fcte-pi1/2026_1_PI1_Grupo02_Bruno/hw/Divisor de Tensão/EsquematicoDivisorDeTensao.png

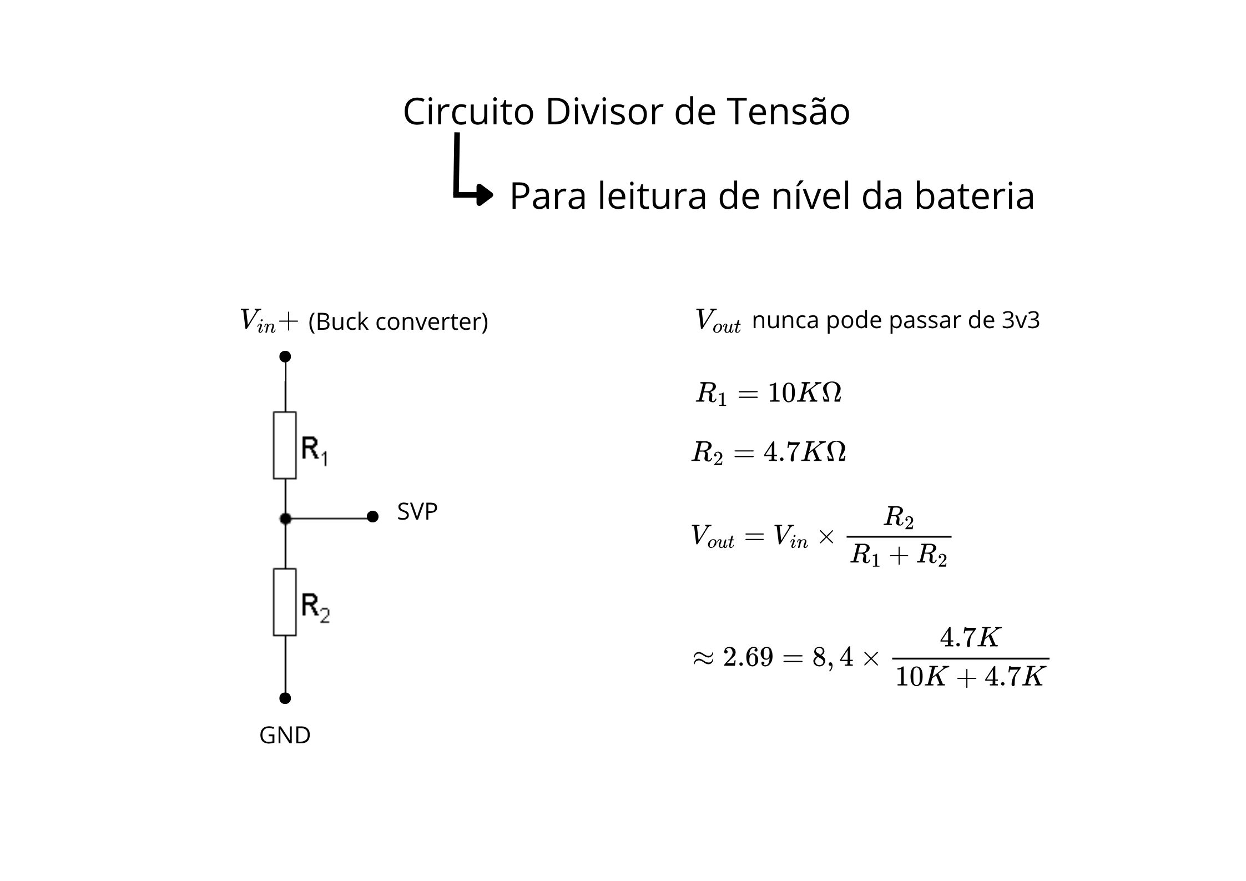
hw/Divisor de Tensão/EsquematicoDivisorDeTensao.png
