fcte-pi1/2026_1_PI1_Grupo02_Bruno/hw/esquematico_geral.png

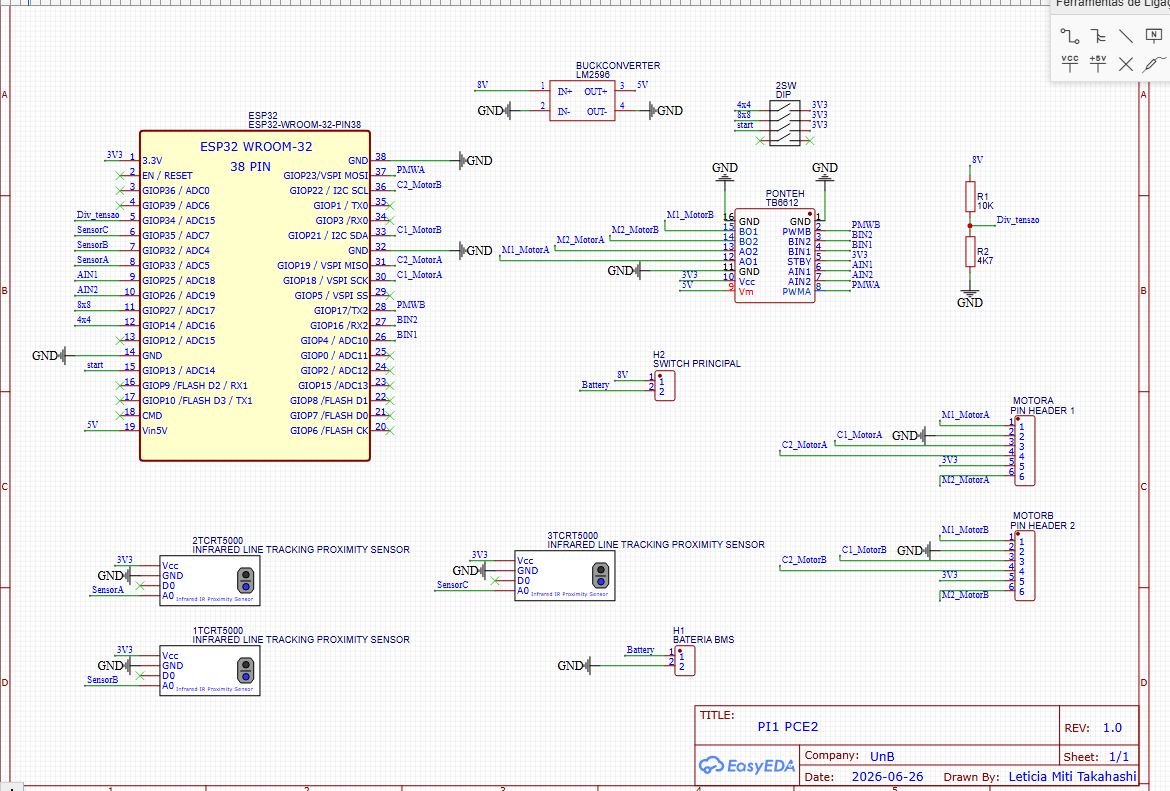
hw/esquematico_geral.png
