fcte-pi1/2026_1_PI1_Grupo02_Bruno/hw/Update na Lógica de Alimentação/EsquematicoSwitchMestre.png

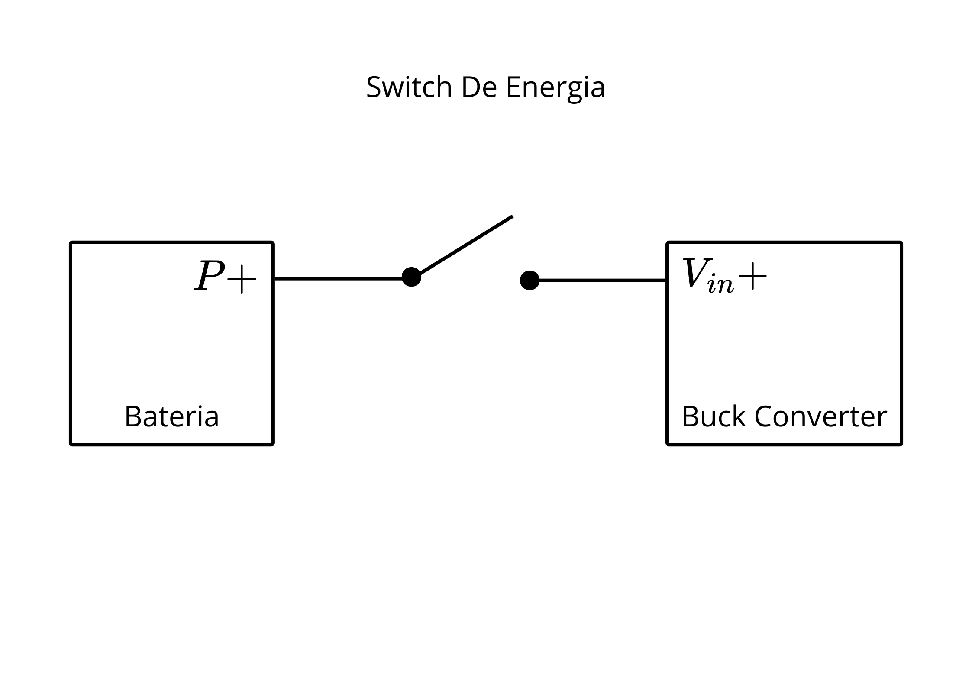
hw/Update na Lógica de Alimentação/EsquematicoSwitchMestre.png
