fcte-pi1/2026_1_PI1_Grupo02_Bruno/mec/Robô/media/chassi e rodas.jpeg

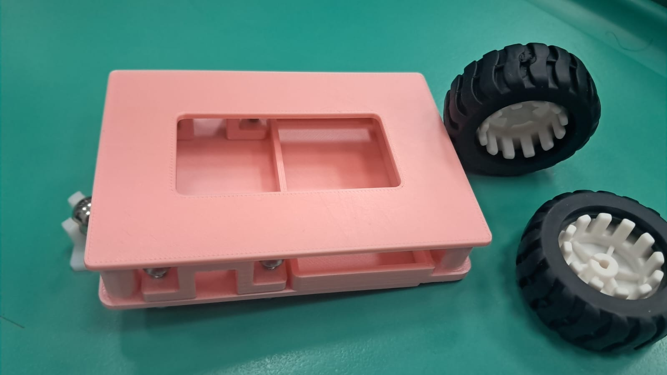
mec/Robô/media/chassi e rodas.jpeg
