fcte-pi1/2026_1_PI1_Grupo02_Bruno/mec/Robô/media/Chassi parafusado.jpeg

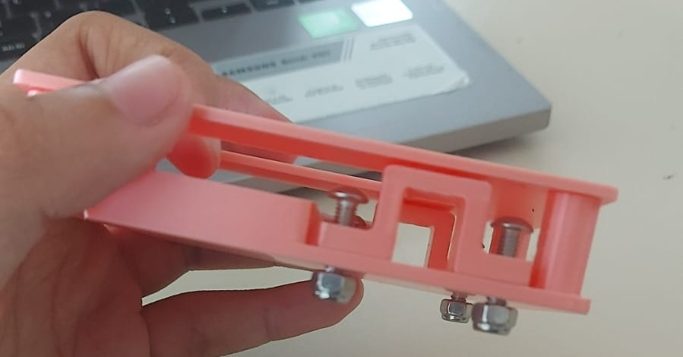
mec/Robô/media/Chassi parafusado.jpeg
