fcte-pi1/2026_1_PI1_Grupo02_Bruno/hw/Componentes/Comprovantes dos Componentes/ComprovanteESP.jpeg

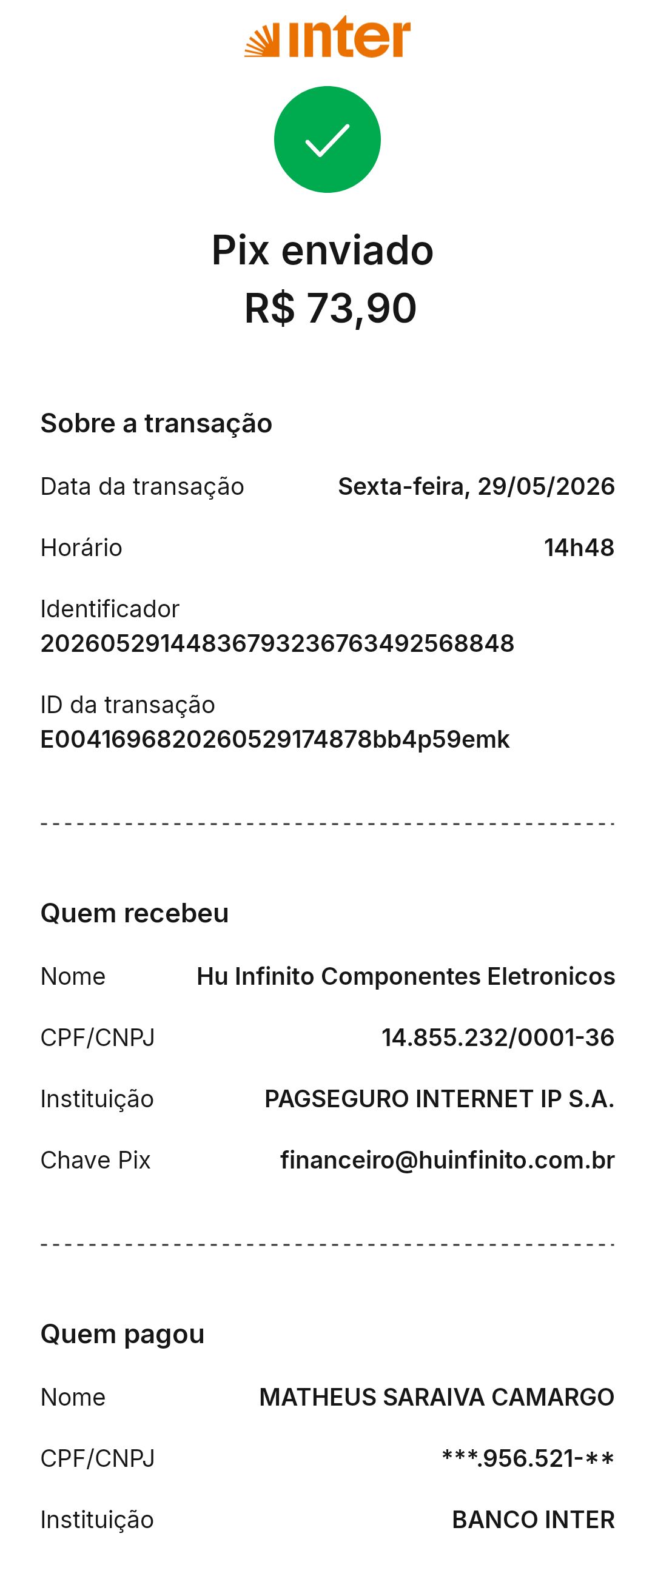
hw/Componentes/Comprovantes dos Componentes/ComprovanteESP.jpeg
