fcte-pi1/2026_1_PI1_Grupo02_Bruno/hw/Componentes/ModeloESP32.jpg

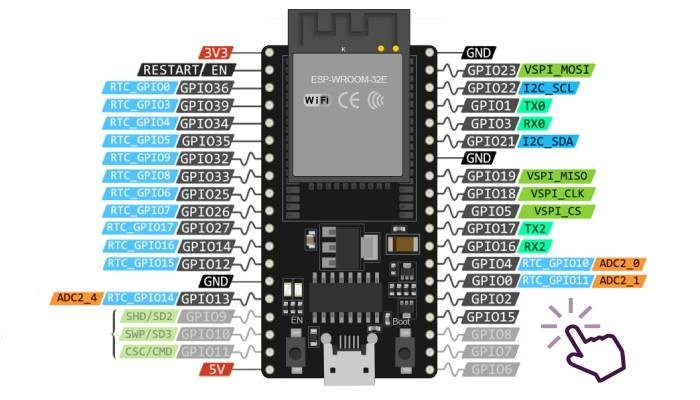
hw/Componentes/ModeloESP32.jpg
