fcte-pi1/2026_1_PI1_Grupo02_Bruno/hw/Teste De Alimentação/EsquematicoAlimentacao.png

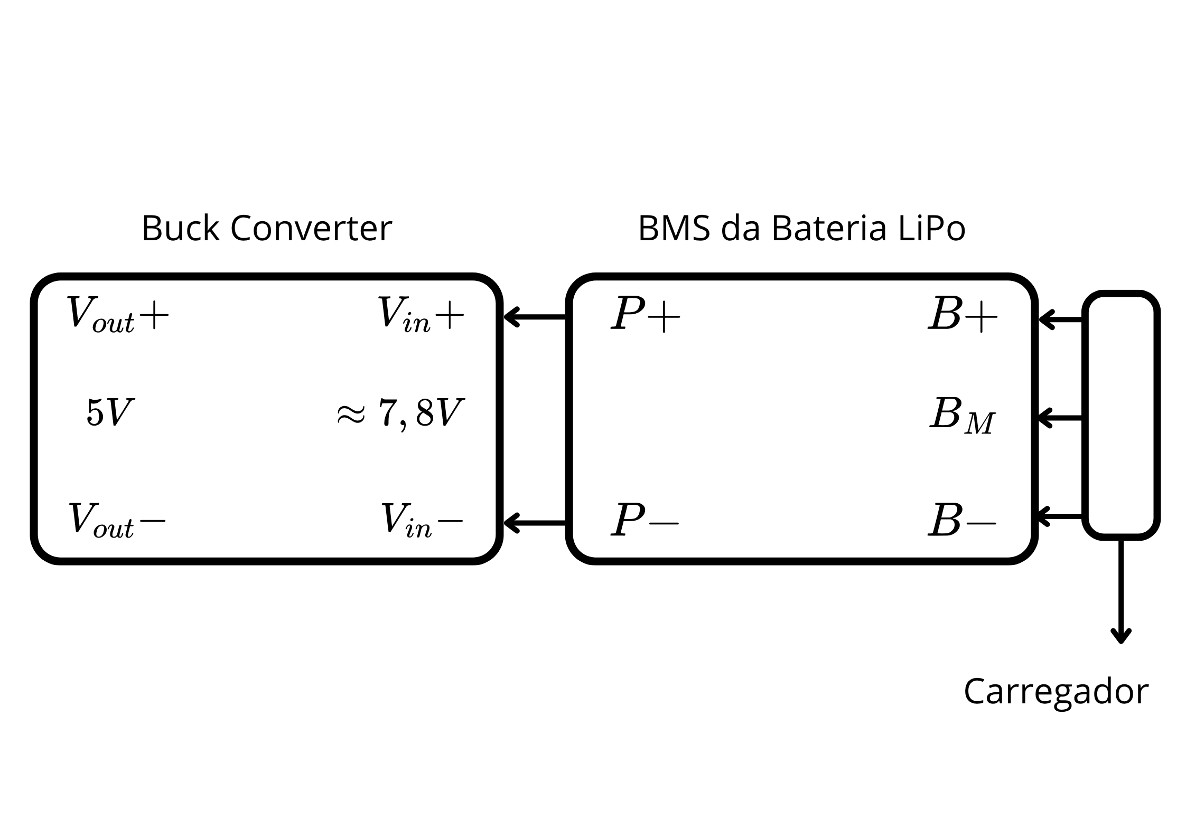
hw/Teste De Alimentação/EsquematicoAlimentacao.png
