fcte-pi1/2026_1_PI1_Grupo02_Bruno/hw/Teste dos Motores, Encoders e Ponte H/Esquematico_Motores_E_PonteH.png

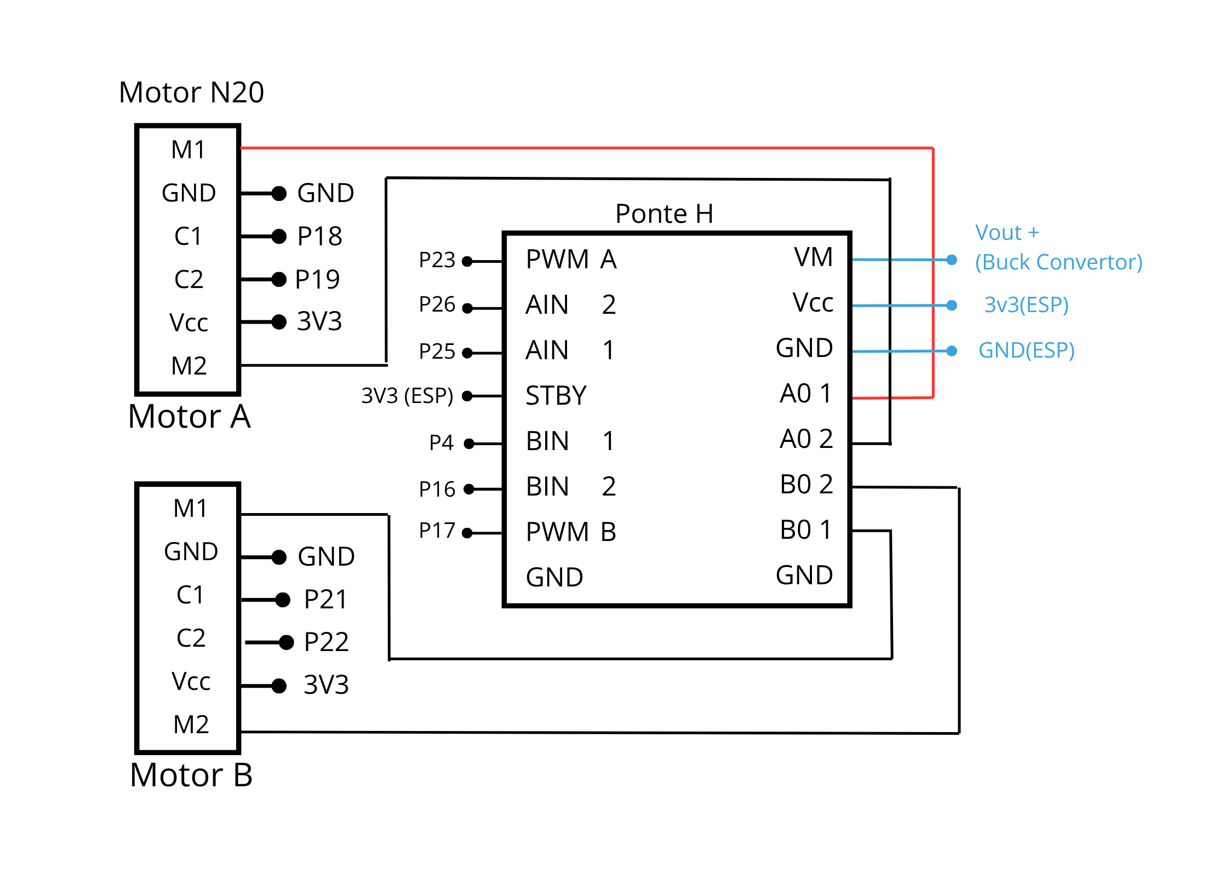
hw/Teste dos Motores, Encoders e Ponte H/Esquematico_Motores_E_PonteH.png
