fcte-pi1/2026_1_PI1_Grupo02_Bruno/hw/Mapeamento da ESP/EsquematicoESP.pdf

5V

## CND

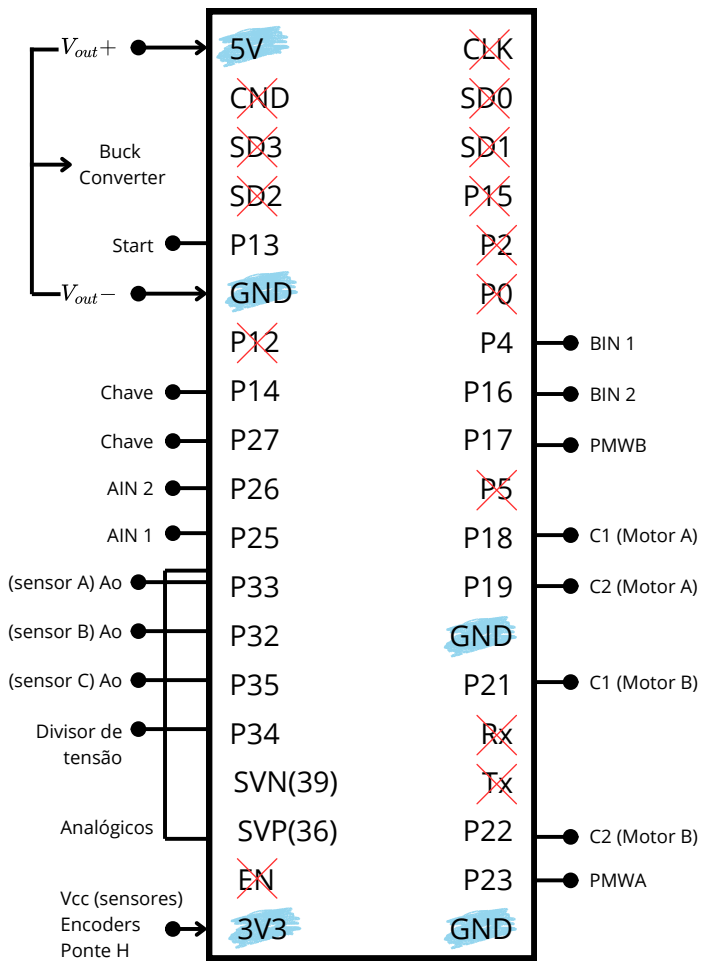
[picture p49: page 1]
