fcte-pi1/2026_1_PI1_Grupo02_Bruno/hw/Mapeamento da ESP/PortasAnalogicas.pdf

## Portas Analógicas

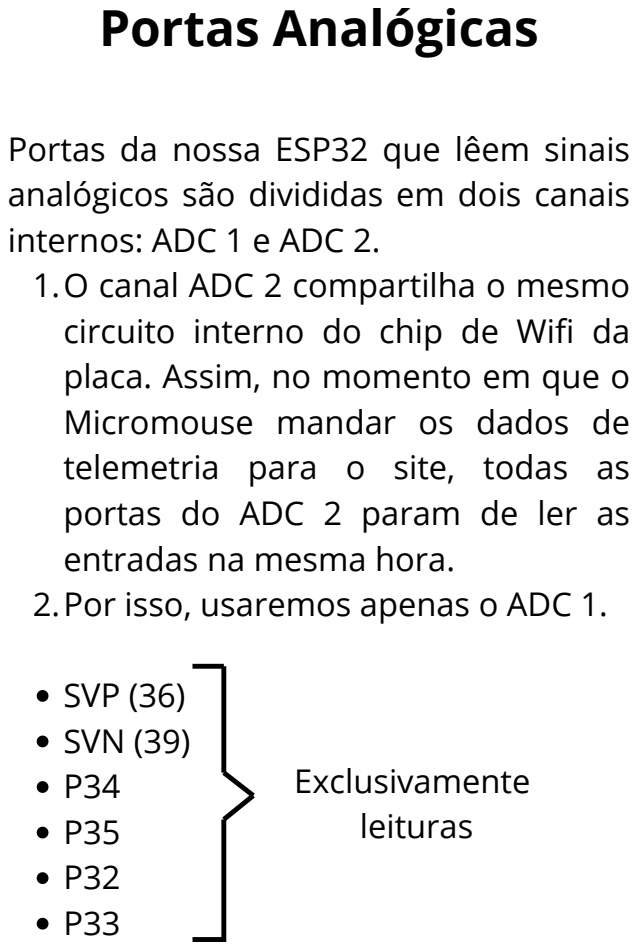
[picture p50: page 1]
SVP (36) SVN (39) P34 P35 P32 P33; Exclusivamente leituras

Portas da nossa ESP32 que lêem sinais
analógicos são divididas em dois canais
internos: ADC 1 e ADC 2.
1.O canal ADC 2 compartilha o mesmo
circuito interno do chip de Wifi da
placa. Assim, no momento em que o
Micromouse mandar os dados de
telemetria para o site, todas as
portas do ADC 2 param de ler as
entradas na mesma hora.
2.Por isso, usaremos apenas o ADC 1.
