fcte-pi1/2026_1_PI1_Grupo02_Bruno/mec/Desenho Técnico/Robô/Explode_Sheet_1.pdf

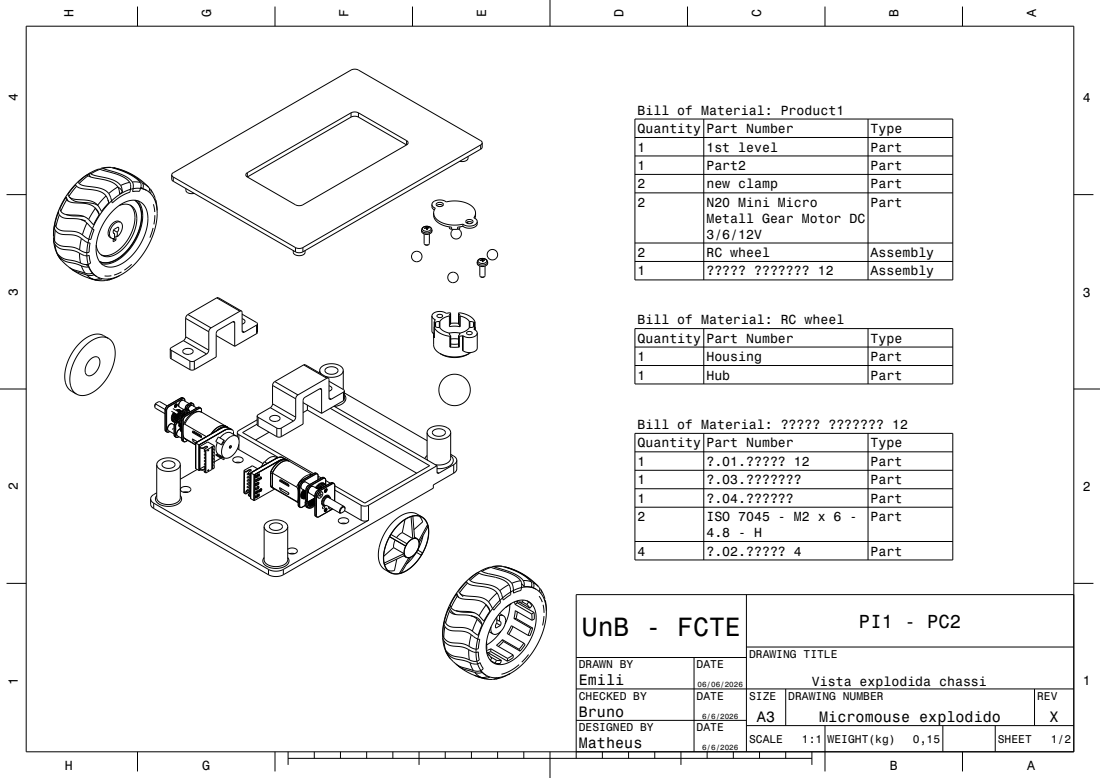
[picture p51: page 1]
DRAWING TITLE; UnB - FCTE

Bill of Material: Product1

Quantity | Part Number | Type
1 | 1st level | Part
1 | Part2 | Part
2 | new clamp | Part
2 | N20 Mini Micro Metall Gear Motor DC 3/6/12V | Part

2 | RC wheel | Assembly
1 | ????? ??????? 12 | Assembly

Bill of Material: RC wheel

1 | Housing | Part
1 | Hub | Part

Bill of Material: ????? ??????? 12

1 | ?.01.????? 12 | Part
1 | ?.03.??????? | Part
1 | ?.04.?????? | Part
2 | ISO 7045 - M2 x 6 -4.8 - H | Part

4 | ?.02.????? 4 | Part

DRAWN BY Emili | DATE 06/06/2026

Vista explodida chassi

CHECKED BY Bruno | DATE 6/6/2026 | SIZE A3 | DRAWING NUMBER Micromouse explodido | REV X

DESIGNED BY Matheus | DATE 6/6/2026

SCALE 1:1 | WEIGHT(kg) 0,15 | SHEET 1/2
