fcte-pi1/2026_1_PI1_Grupo02_Bruno/mec/Desenho Técnico/Labirinto/Labirinto Draft.pdf

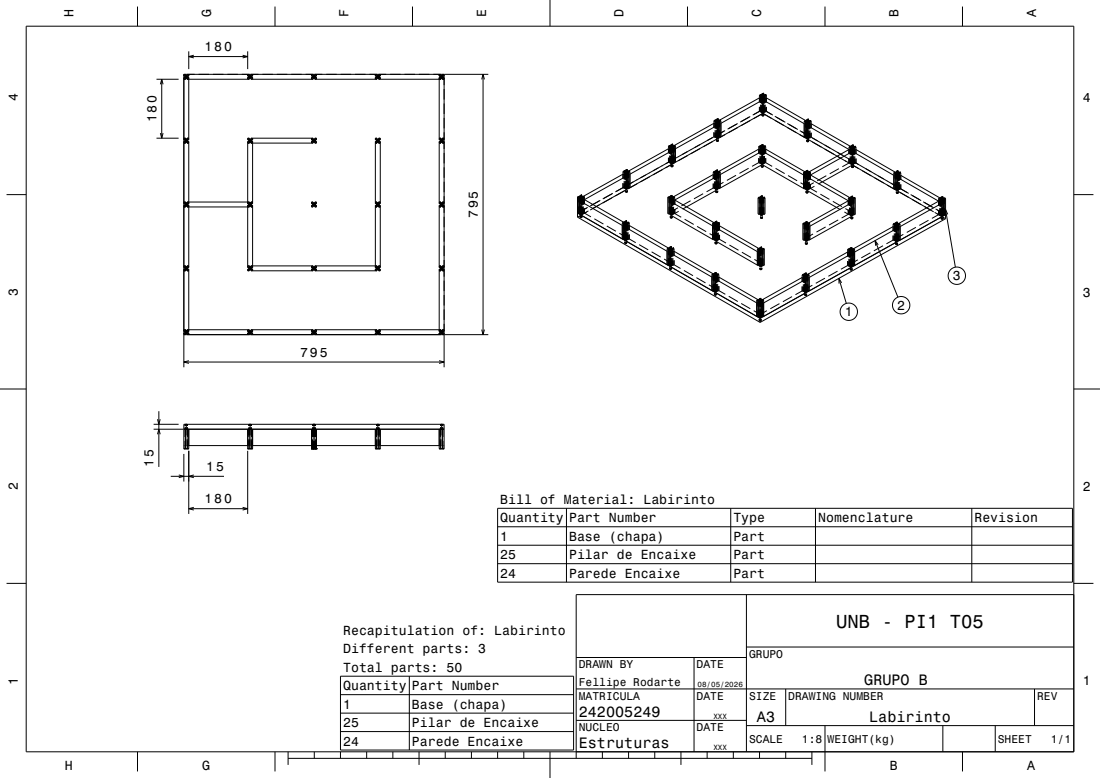
[picture p52: page 1]
DRAWN BY Fellipe Rodarte; SCALE; 1:8 WEIGHT(kg); SHEET; DRAWING NUMBER; Quantity Part Number; Type; Nomenclature; Revision; Base (chapa); Part; Pilar de Encaixe; Parede Encaixe; GRUPO B; UNB - PI1 T05

Bill of Material: Labirinto

Recapitulation of: Labirinto
Different parts: 3
Total parts: 50
Quantity Part Number
