fcte-pi1/2026_1_PI1_Grupo02_Bruno/mec/Desenho Técnico/Robô/Drafting roda.pdf

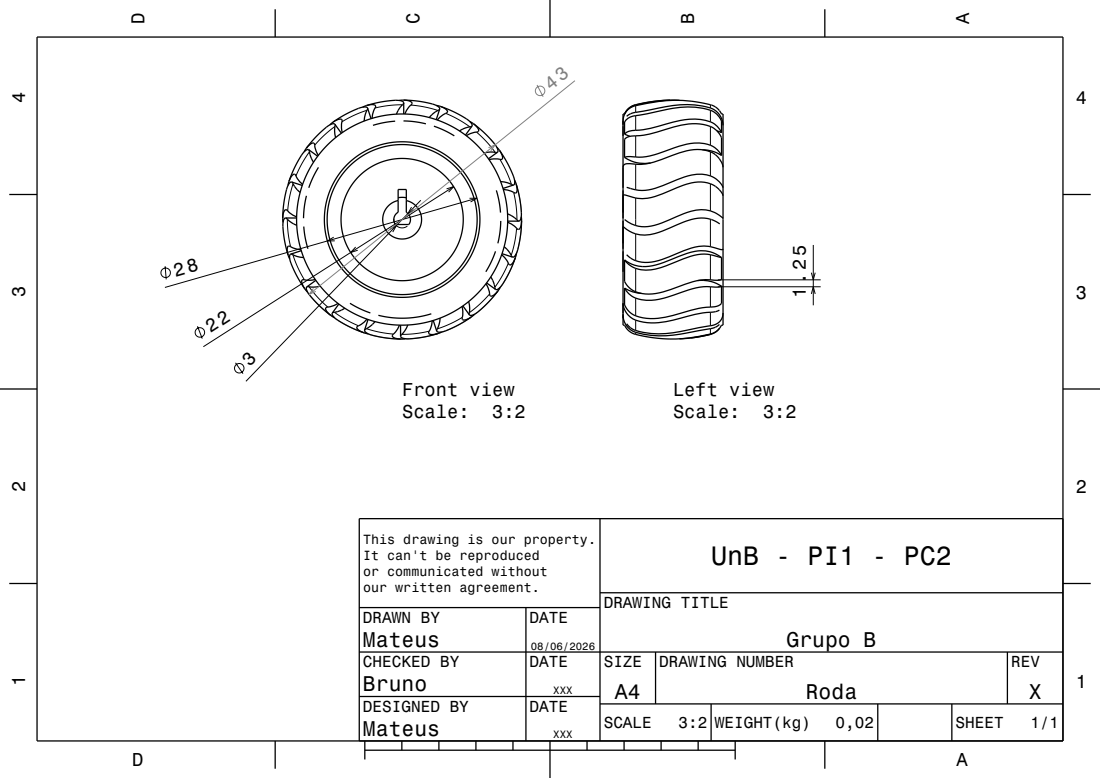
[picture p53: page 1]
DRAWING TITLE; Grupo B; UnB - PI1 - PC2; Front view Scale: 3:2; Left view; Scale: 3:2 1.25

This drawing is our property.
It can't be reproduced
or communicated without
our written agreement.

DRAWN BY Mateus | DATE 08/06/2026

CHECKED BY Bruno | DATE XXX | SIZE A4 | DRAWING NUMBER Roda | REV X

DESIGNED BY Mateus | DATE XXX

SCALE 3:2 | WEIGHT(kg) 0,02 | SHEET 1/1
