fcte-pi1/2026_1_PI1_Grupo02_Bruno/mec/Desenho Técnico/Labirinto/Base (chapa) Draft.pdf

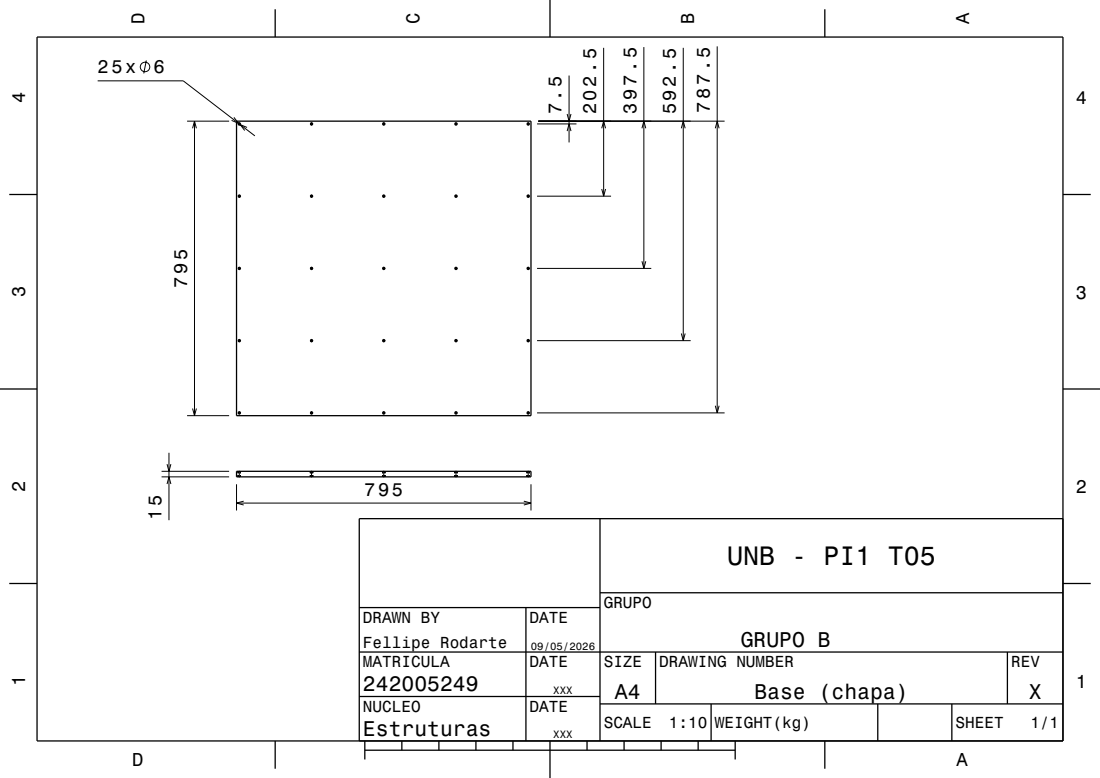
[picture p54: page 1]
UNB - PI1 T05; GRUPO B

DRAWN BY Fellipe Rodarte | DATE 09/05/2026

MATRICULA 242005249 | DATE XXX | SIZE A4 | DRAWING NUMBER Base (chapa) | REV X

NUCLEO Estruturas | DATE XXX

SCALE 1:10 | WEIGHT(kg) | SHEET 1/1
