fcte-pi1/2026_1_PI1_Grupo02_Bruno/hw/Projeto Conceitual de Eletrônica ED1/esquematico_ED1.kicad_sch

## KiCad design hw/Projeto Conceitual de Eletrônica ED1/esquematico_ED1.kicad_sch (2026-05-20)

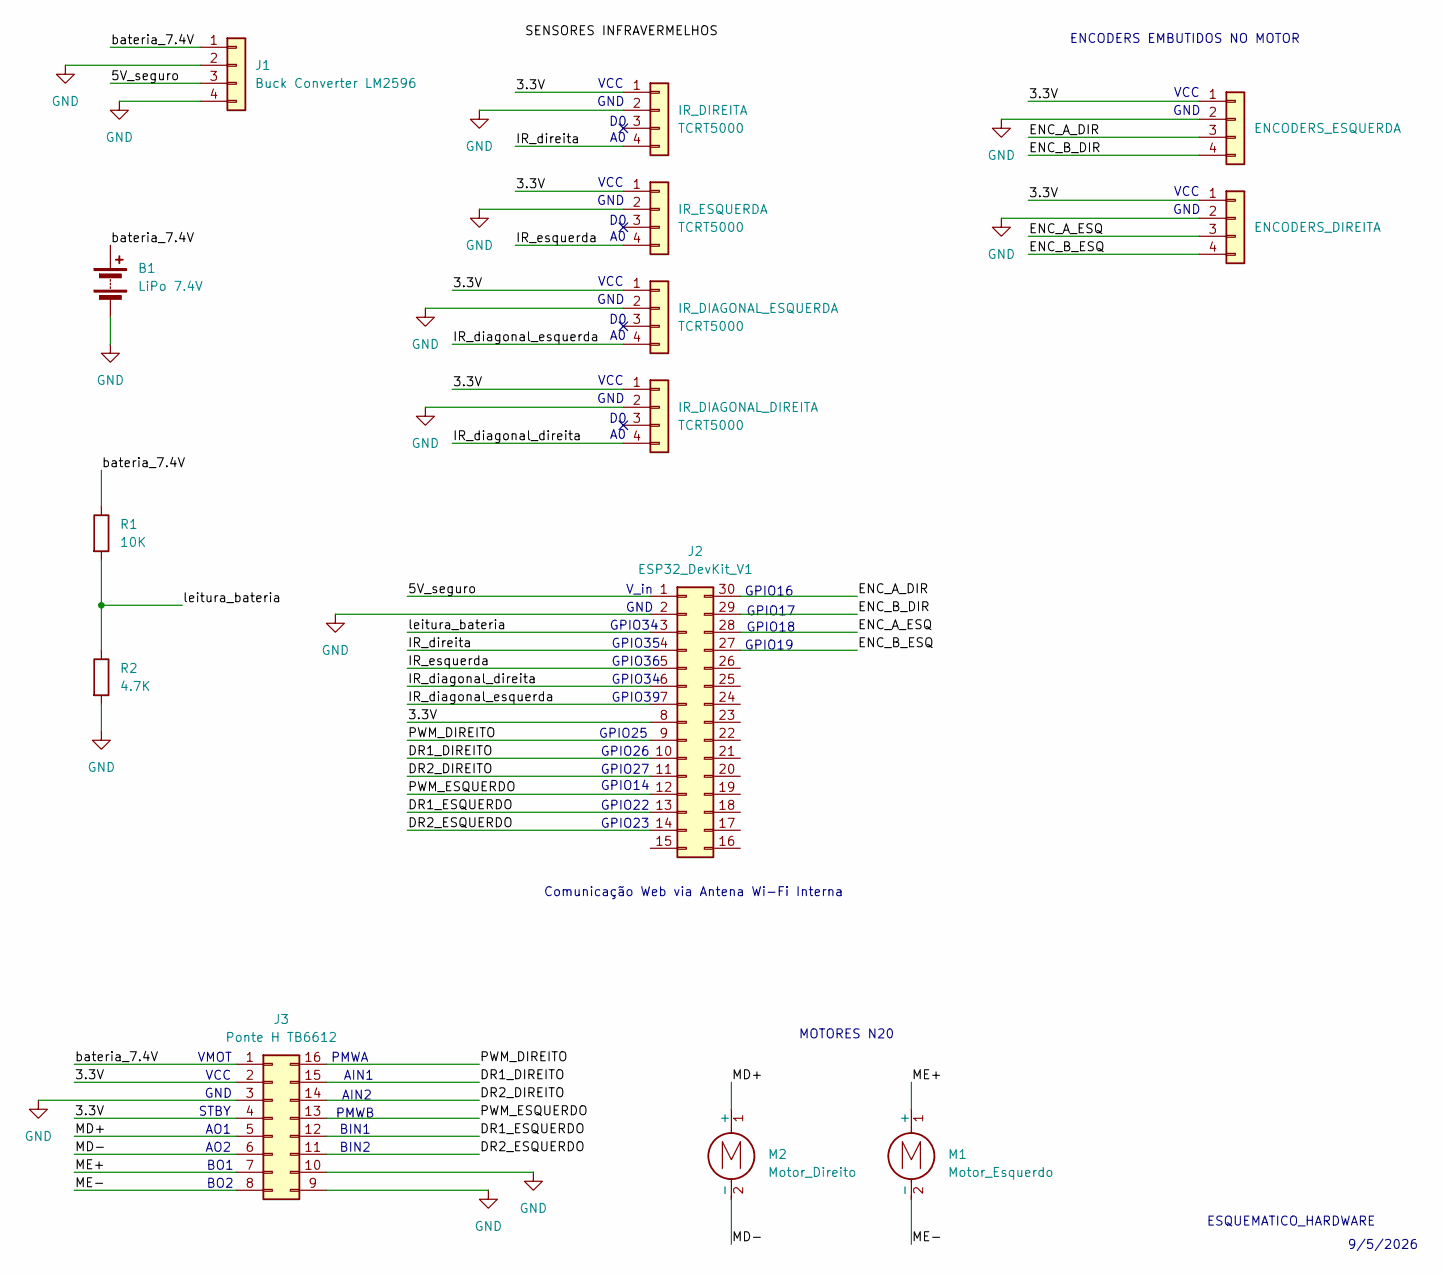
[picture p56: schematic esquematico_ED1.kicad_sch]

Parts:
B1: LiPo 7.4V
ENCODERS_DIREITA: (no value)
ENCODERS_ESQUERDA: (no value)
IR_DIAGONAL_DIREITA: TCRT5000
IR_DIAGONAL_ESQUERDA: TCRT5000
IR_DIREITA: TCRT5000
IR_ESQUERDA: TCRT5000
J1: Buck Converter LM2596
J2: ESP32_DevKit_V1
J3: Ponte H TB6612
M1: Motor_Esquerdo
M2: Motor_Direito
R1: 10K
R2: 4.7K

Connections:
3.3V: ENCODERS_DIREITA.1, ENCODERS_ESQUERDA.1, IR_DIAGONAL_DIREITA.1, IR_DIAGONAL_ESQUERDA.1, IR_DIREITA.1, IR_ESQUERDA.1, J2.8, J3.2, J3.4
5V_seguro: J1.3, J2.1
DR1_DIREITO: J2.10, J3.15
DR1_ESQUERDO: J2.13, J3.12
DR2_DIREITO: J2.11, J3.14
DR2_ESQUERDO: J2.14, J3.11
ENC_A_DIR: ENCODERS_ESQUERDA.3, J2.30
ENC_A_ESQ: ENCODERS_DIREITA.3, J2.28
ENC_B_DIR: ENCODERS_ESQUERDA.4, J2.29
ENC_B_ESQ: ENCODERS_DIREITA.4, J2.27
GND: B1.2 (-), ENCODERS_DIREITA.2, ENCODERS_ESQUERDA.2, IR_DIAGONAL_DIREITA.2, IR_DIAGONAL_ESQUERDA.2, IR_DIREITA.2, IR_ESQUERDA.2, J1.2, J1.4, J2.2, J3.3, J3.9, J3.10, R2.2
IR_diagonal_direita: IR_DIAGONAL_DIREITA.4, J2.6
IR_diagonal_esquerda: IR_DIAGONAL_ESQUERDA.4, J2.7
IR_direita: IR_DIREITA.4, J2.4
IR_esquerda: IR_ESQUERDA.4, J2.5
MD+: J3.5, M2.1 (+)
MD-: J3.6, M2.2 (-)
ME+: J3.7, M1.1 (+)
ME-: J3.8, M1.2 (-)
PWM_DIREITO: J2.9, J3.16
PWM_ESQUERDO: J2.12, J3.13
bateria_7.4V: B1.1 (+), J1.1, J3.1, R1.1
leitura_bateria: J2.3, R1.2, R2.1

Notes on the sheet:
GND
GPIO39
AO1
VCC
GPIO34
GPIO25
V_in
AIN1
GPIO35
STBY
GPIO36
BIN2
GPIO27
BO1
GPIO22
VMOT
GPIO19
PMWA
MOTORES N20
ESQUEMATICO_HARDWARE
GPIO26
BO2
AO2
ENCODERS EMBUTIDOS NO MOTOR
GPIO14
PMWB
Comunicação Web via Antena Wi-Fi Interna
GPIO18
GPIO23
GPIO17
BIN1
AIN2
GPIO16
9/5/2026
